Rov-10/kurumachi/firmware/kurumachi/src/bitmaps.h

#pragma once
#include <pgmspace.h>

const unsigned char car_front_bmp[] PROGMEM = {
  0x00,0x00,0x00,0x00, 0x00,0x00,0x00,0x00,
  0x00,0x00,0x00,0x00, 0x00,0x00,0x00,0x00,
  0x00,0x00,0x00,0x00, 0x00,0x00,0x00,0x00,
  0x00,0x00,0x00,0x00, 0x00,0xFE,0xFF,0x00,
  0x00,0xFF,0xFF,0x01, 0x80,0x01,0x00,0x03,
  0x80,0x01,0x00,0x03, 0x80,0x00,0x00,0x02,
  0xC0,0x00,0x00,0x06, 0xF0,0xFF,0xFF,0x1F,
  0xF0,0xFF,0xFF,0x1F, 0xF0,0xFF,0xFF,0x1F,
  0xE0,0xFE,0xFF,0x0E, 0x60,0xF8,0x3F,0x0C,
  0x60,0xF0,0x1F,0x0C, 0xE0,0xF8,0x3F,0x0E,
  0xE0,0xFF,0xFF,0x0F, 0xE0,0xFF,0xFF,0x0F,
  0xE0,0xFF,0xFF,0x0F, 0xE0,0x01,0x00,0x0F,
  0xE0,0x01,0x00,0x0F, 0xE0,0x00,0x00,0x0E,
  0x00,0x00,0x00,0x00, 0x00,0x00,0x00,0x00,
  0x00,0x00,0x00,0x00, 0x00,0x00,0x00,0x00,
  0x00,0x00,0x00,0x00, 0x00,0x00,0x00,0x00
};

const unsigned char car_side_bmp[] PROGMEM = {
  0x00,0x00,0x00,0x00, 0x00,0x00,0x00,0x00,
  0x00,0x00,0x00,0x00, 0x00,0x00,0x00,0x00,
  0x00,0x00,0x00,0x00, 0x00,0x00,0x00,0x00,
  0x00,0x00,0x00,0x00, 0x00,0x00,0x00,0x00,
  0x00,0x00,0x00,0x00, 0x00,0x00,0x00,0x00,
  0x00,0x00,0x00,0x00, 0x00,0x00,0xFF,0x07,
  0x00,0x60,0x10,0x1C, 0x00,0x18,0x10,0x78,
  0x00,0x3E,0x10,0xF8, 0xF0,0xFF,0xFF,0xFF,
  0x1C,0xFF,0xFF,0xE3, 0xE6,0xFE,0xFF,0xDD,
  0xB6,0xFC,0xFF,0xBE, 0xF6,0xFD,0xFF,0xBE,
  0x96,0xFD,0xFF,0xBE, 0xF0,0x00,0x00,0x1C,
  0x00,0x00,0x00,0x00, 0x00,0x00,0x00,0x00,
  0x00,0x00,0x00,0x00, 0x00,0x00,0x00,0x00,
  0x00,0x00,0x00,0x00, 0x00,0x00,0x00,0x00,
  0x00,0x00,0x00,0x00, 0x00,0x00,0x00,0x00,
  0x00,0x00,0x00,0x00, 0x00,0x00,0x00,0x00
};
